makerstorage/WiFi-Temp/firmware/esp/htmlEmbed.h

/*
myWebServer.cpp for esp8266

Copyright (c) 2016 David Paiva (david@nailbuster.com). All rights reserved.


This library is free software; you can redistribute it and/or
modify it under the terms of the GNU Lesser General Public
License as published by the Free Software Foundation; either
version 2.1 of the License, or (at your option) any later version.
This library is distributed in the hope that it will be useful,
but WITHOUT ANY WARRANTY; without even the implied warranty of
MERCHANTABILITY or FITNESS FOR A PARTICULAR PURPOSE.  See the GNU
Lesser General Public License for more details.
You should have received a copy of the GNU Lesser General Public
License along with this library; if not, write to the Free Software
Foundation, Inc., 51 Franklin St, Fifth Floor, Boston, MA  02110-1301  USA
*/

#ifndef _HTMLEMBED_h
#define _HTMLEMBED_h

#if defined(ARDUINO) && ARDUINO >= 100
	#include "Arduino.h"
#else
	#include "WProgram.h"
#endif


/* Stores default pages for WIFI setup and FSBrowse for initial setup.
//
//  these at GZ versions of html files that I used bin2header.exe on to create header....
//
//const char PAGE_WIFISETUP[] PROGMEM = R"=====(
//
//const char PAGE_FSBROWSE[] PROGMEM = R"=====(
*/

const char PAGE_FSBROWSE[] PROGMEM = {
    0x1f, 0x8b, 0x08, 0x08, 0x4d, 0xff, 0xaf, 0x56, 0x02, 0x00, 0x66, 0x69, 
    0x6c, 0x65, 0x62, 0x72, 0x6f, 0x77, 0x73, 0x65, 0x2e, 0x68, 0x74, 0x6d, 
    0x6c, 0x00, 0xad, 0x1b, 0x67, 0x7a, 0xea, 0x46, 0xf0, 0x77, 0x7c, 0x0a, 
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
    0xcb, 0x8e, 0x53, 0x2d, 0x15, 0x14, 0x18, 0xa3, 0x5e, 0x30, 0xa5, 0xe0, 
    0x7e, 0xfc, 0x2d, 0x9a, 0x92, 0x74, 0xdb, 0x6a, 0x2b, 0x66, 0x56, 0x63, 
    0x31, 0xaf, 0xae, 0xf5, 0xf4, 0xcd, 0xc9, 0x45, 0x49, 0x99, 0xe2, 0x21, 
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
};



#endif
